micronano0/ESP32-C3-WLAN-Photobooth-Buzzer/bilder/Buzzer_ein_aus.jpg

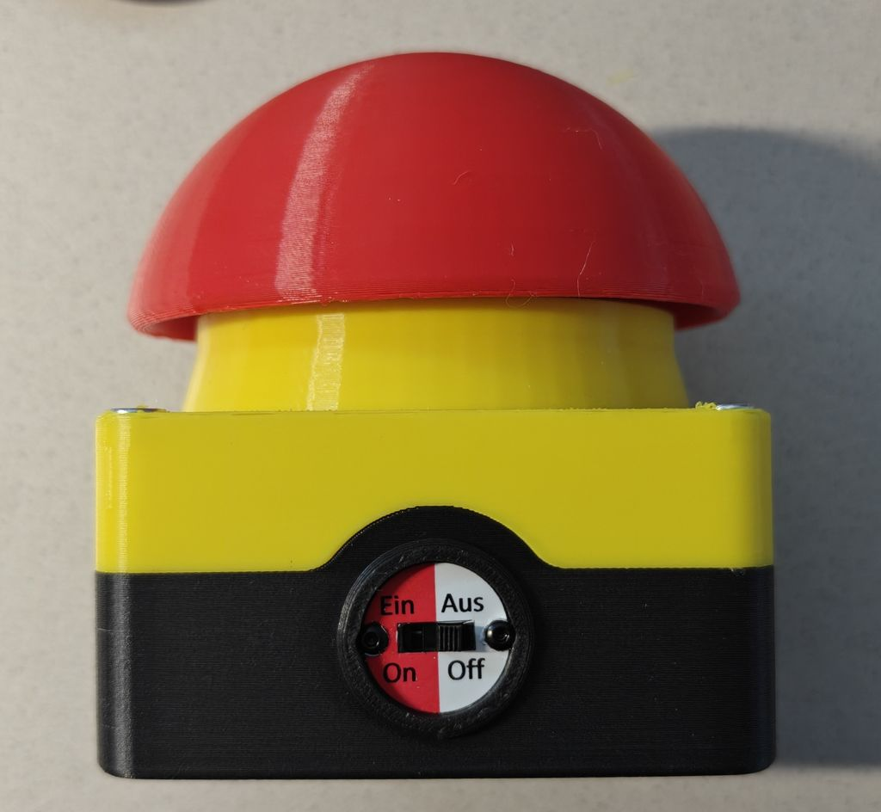
bilder/Buzzer_ein_aus.jpg
