micronano0/ESP32-C3-WLAN-Photobooth-Buzzer/bilder/Buzzer_elektronik_ein_aus.jpg

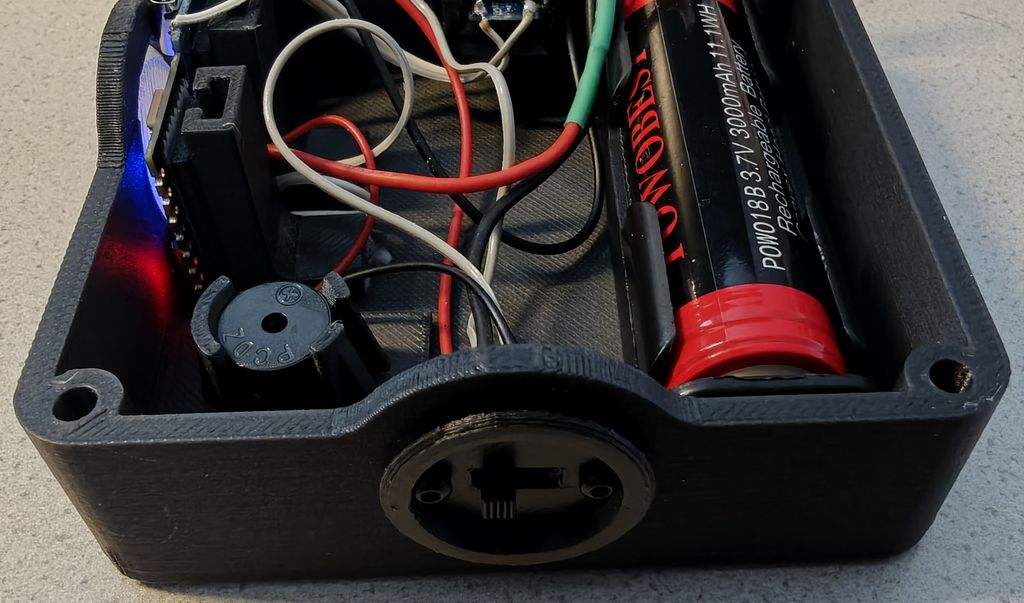
bilder/Buzzer_elektronik_ein_aus.jpg
