micronano0/ESP32-C3-WLAN-Photobooth-Buzzer/bilder/Buzzer_elektronik_usb_c.jpg

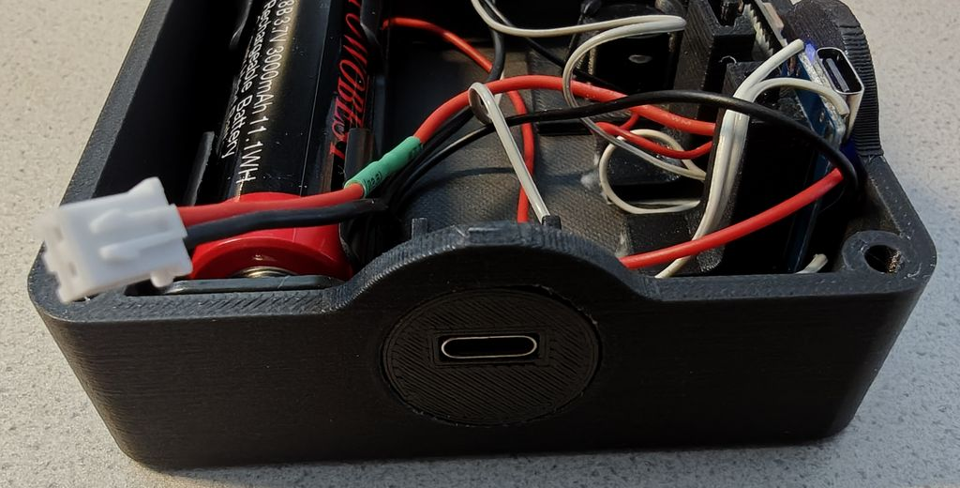
bilder/Buzzer_elektronik_usb_c.jpg
