micronano0/ESP32-C3-WLAN-Photobooth-Buzzer/bilder/buzzer_v2_blender.jpg

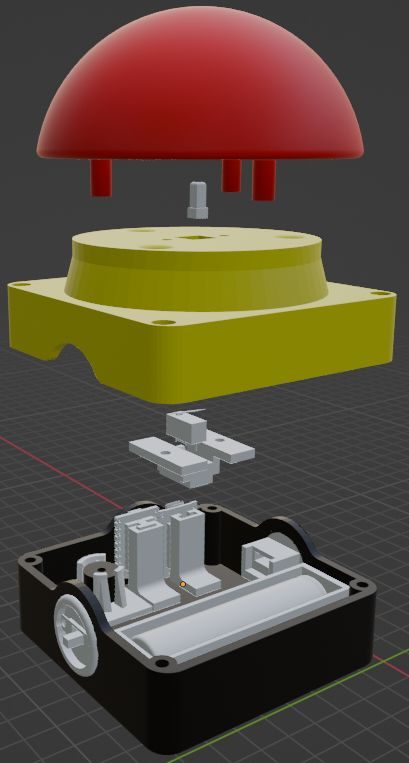
bilder/buzzer_v2_blender.jpg
